DeaDDFuze/DSLITE_Remastered/schematic/original/C-USG-CPU-10.sch

## EAGLE design schematic/original/C-USG-CPU-10.sch (2026-09-28)

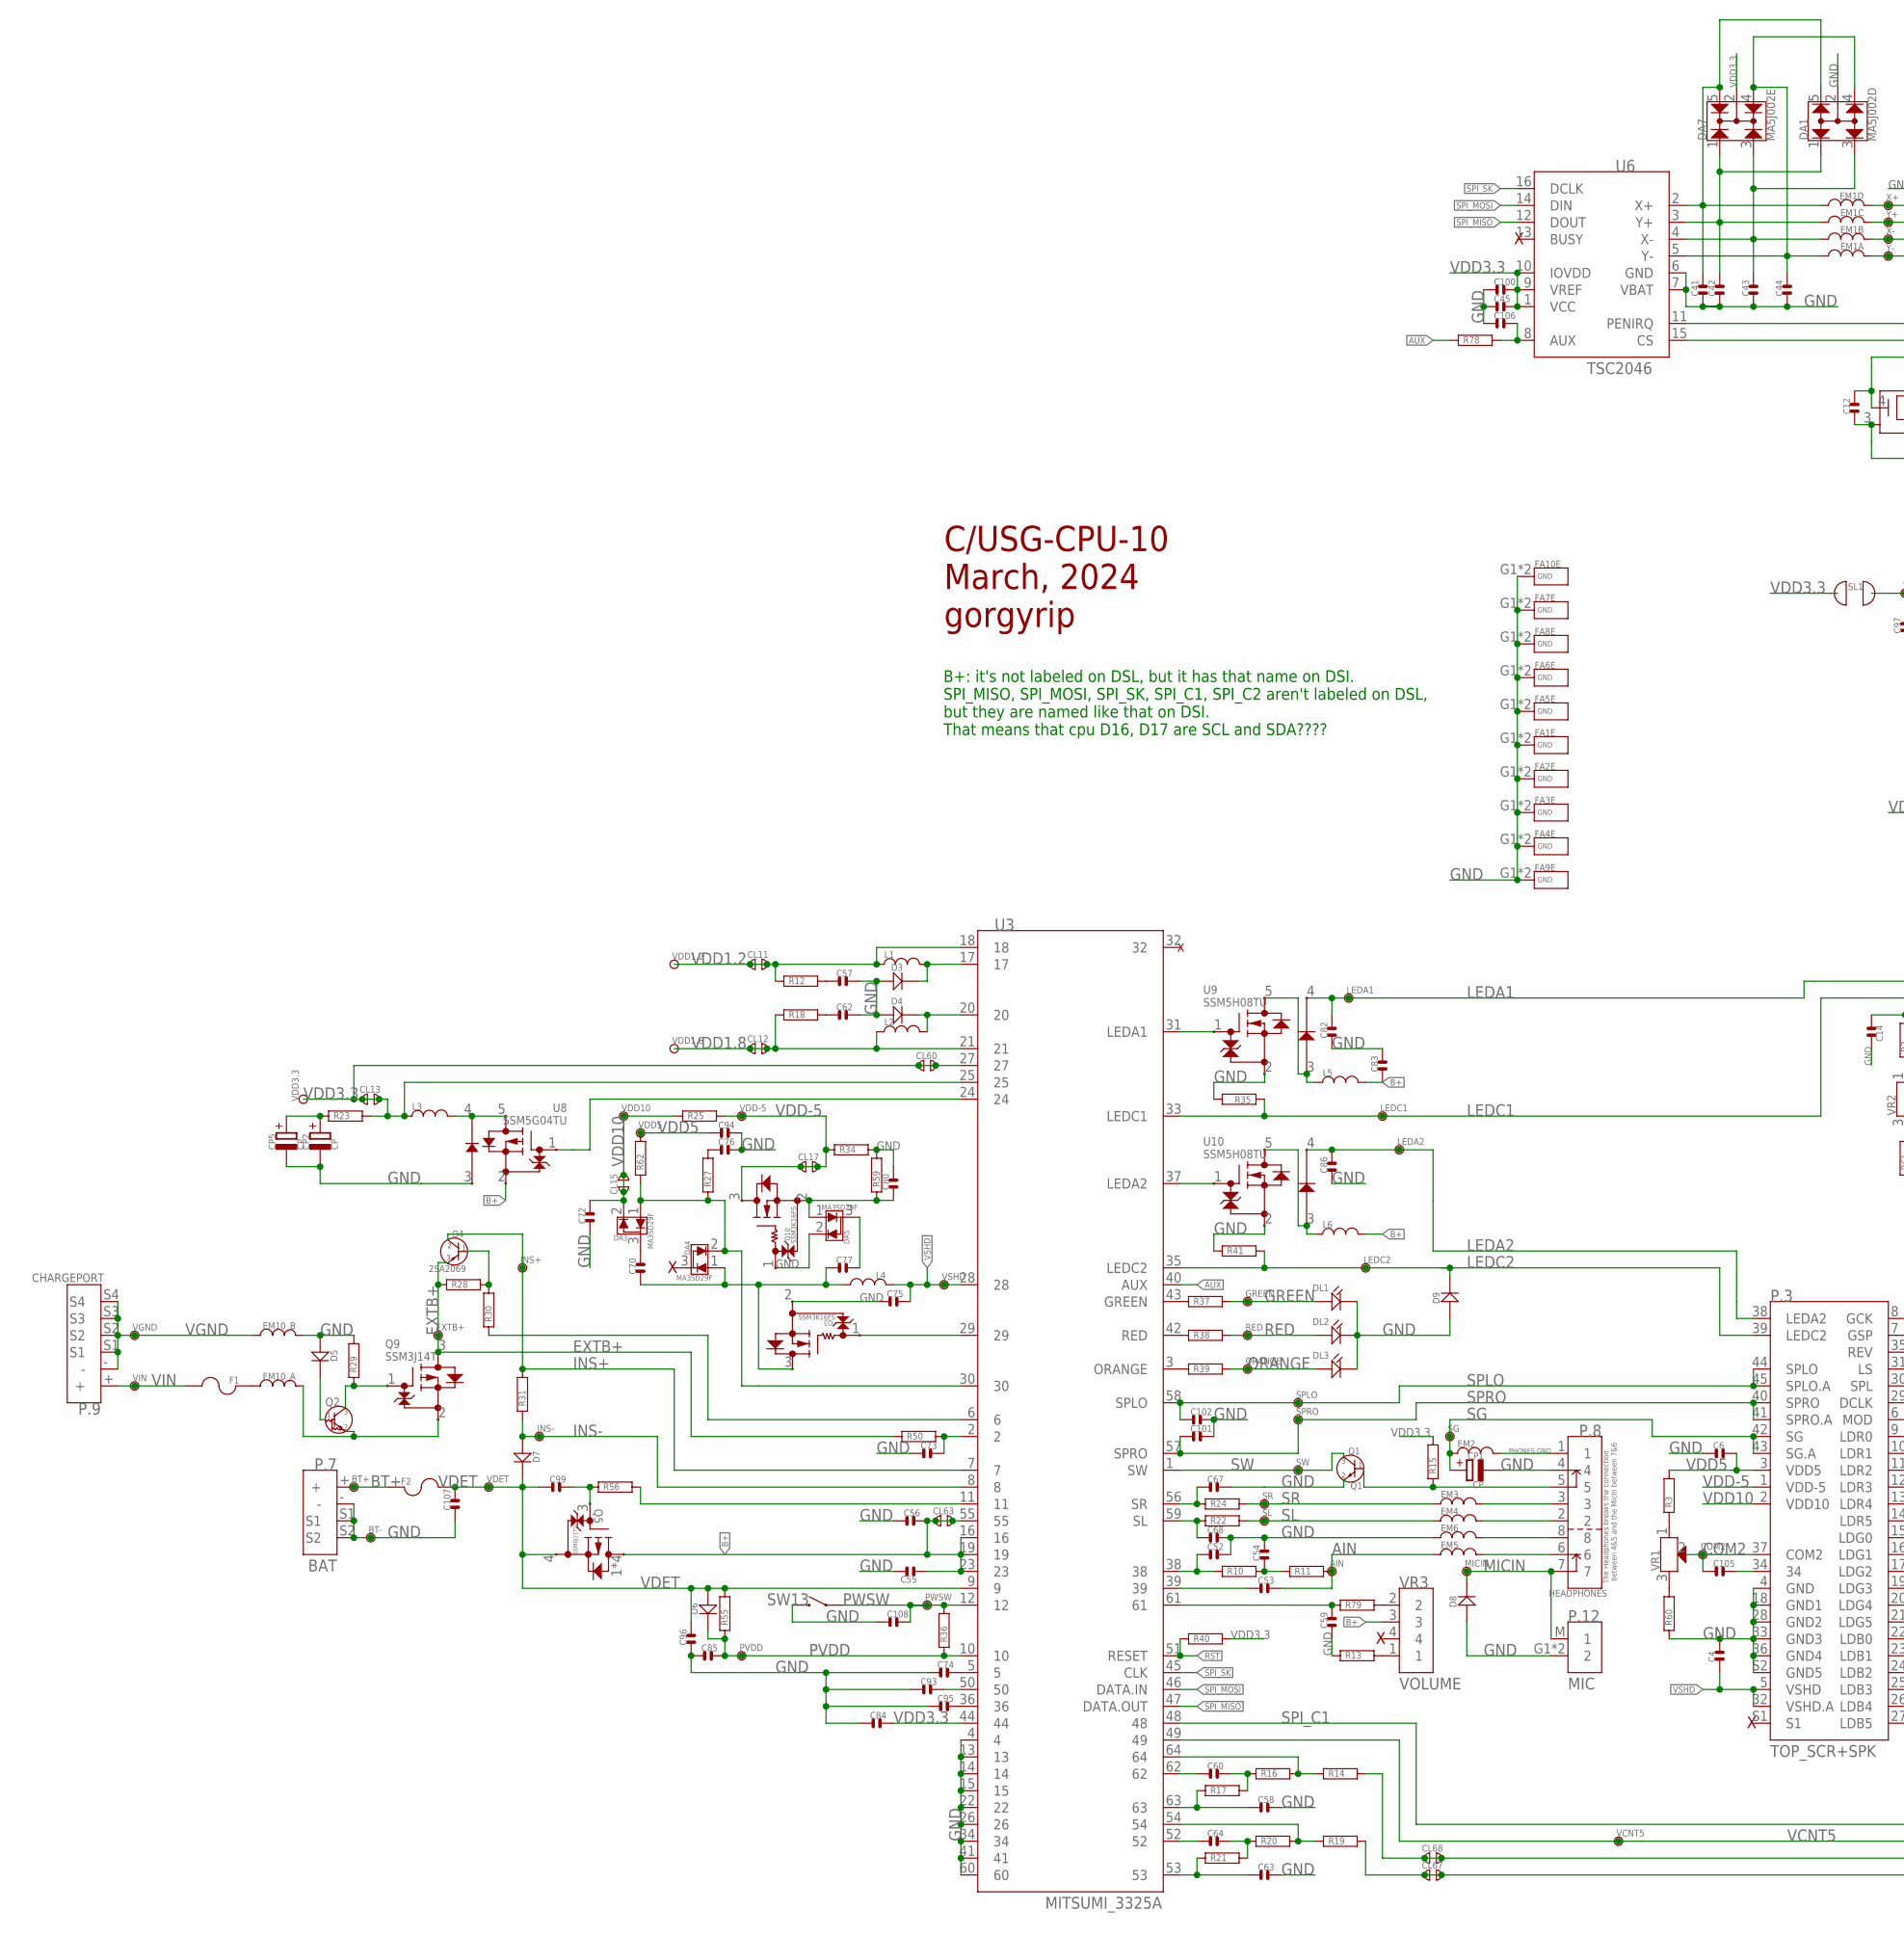
[picture p8: schematic C-USG-CPU-10.sch, part in row 1, column 1]

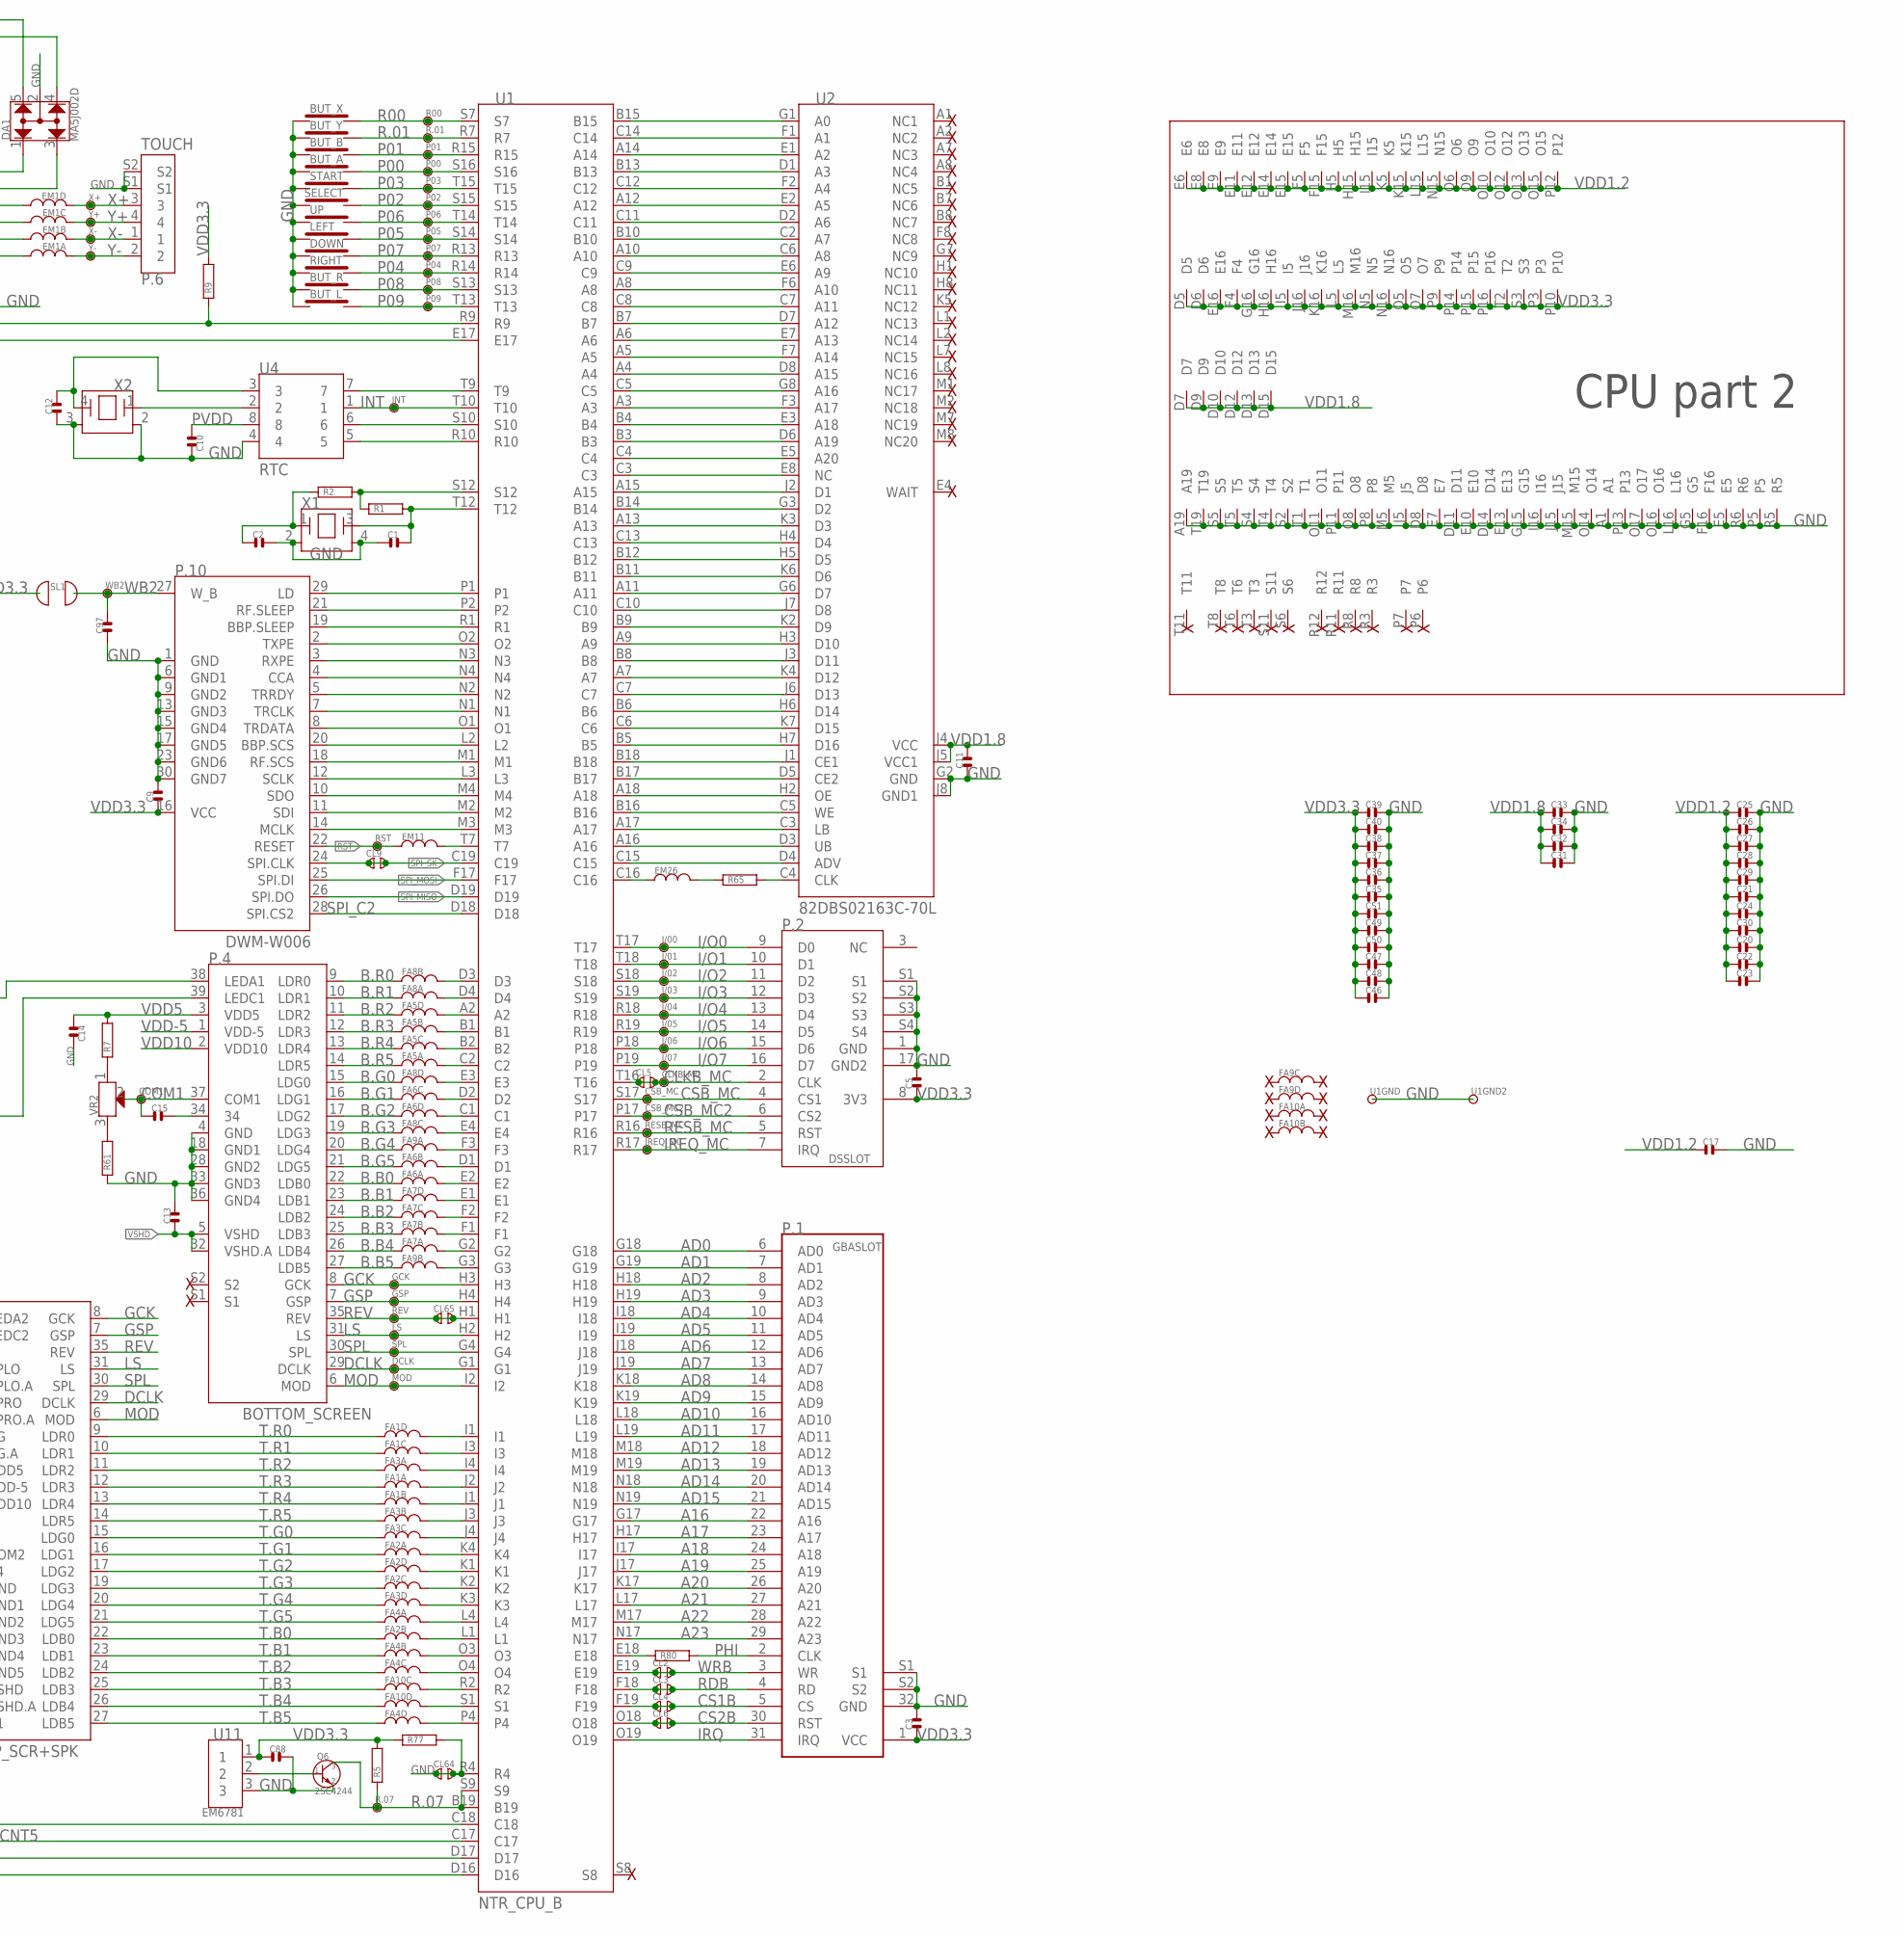
[picture p9: schematic C-USG-CPU-10.sch, part in row 1, column 2]

Parts:
AIN: TP
BT+: TP
BT-: TP
BUT_A: BUT_ABXY; BUTTONSABXY
BUT_B: BUT_ABXY; BUTTONSABXY
BUT_L: SHOULDER_BUT
BUT_R: SHOULDER_BUT
BUT_X: BUT_ABXY; BUTTONSABXY
BUT_Y: BUT_ABXY; BUTTONSABXY
C1, C2, C3, C4, C5, C6, C10, C11, C12, C13, C14, C17, C41, C42, C43, C44, C45, C52, C53, C56, C58, C59, C60, C63, C64, C67, C68, C70, C74, C75, C77, C84, C88, C93, C96, C97, C99, C100, C101, C102, C106, C107, C108: C0402; 0402
C9, C15, C54, C55, C57, C62, C72, C76, C82, C83, C86, C94, C105: C0805; 0805
C20, C21, C22, C23, C24, C25, C26, C27, C28, C29, C30, C31, C32, C33, C34, C35, C36, C37, C38, C39, C40, C46, C47, C48, C49, C50, C51: C0201; 0201
C73, C80, C85, C95: C0603; 0603
CL2, CL3, CL4, CL5, CL6, CL9, CL11, CL12, CL13, CL15, CL17, CL60, CL63, CL64, CL65, CL67, CL68: CL; CL0402
CLKB_MC: TP
COM1, COM2: TP
CP1, CP2, CP5: CP
CSB_MC, CSB_MC2: TP
D3, D4: D3.4
D5, D9: D5
D6: D6
D7: D7
D8: D8
DA1: MA5J002D; DA
DA3, DA4, DA5: MA3SD29F
DA7: MA5J002E; DA
DCLK: TP
DL1, DL2, DL3: DL
DOWN: DPAD
EM1: FILTER_NETWORK
EM2, EM3, EM4, EM5, EM6: FILTER0603; 0603
EM10: EM10
EM11, EM26: FILTER; 0402
EXTB+: TP
F1, F2: FUSE
FA1, FA2, FA3, FA4, FA5, FA6, FA7, FA8, FA9, FA10: FA
GCK: TP
GREEN: TP
GSP: TP
I/00, I/01, I/02, I/03, I/04, I/05, I/06, I/07: TP
INS+: TP
INS-: TP
INT: TP
IREQ_MC: TP
L1, L3, L5, L6: INDUCTOR
L2, L4: INDUCTOR_SMALL
LEDA1, LEDA2: TP
LEDC1, LEDC2: TP
LEFT: DPAD
LS: TP
MICIN: TP
MOD: TP
ORANGE: TP
P00, P01, P02, P03, P04, P05, P06, P07, P08, P09: TP
P.1: GBASLOT; GBA
P.2: DSSLOT; DS
P.3: TOP_SCR+SPK
P.4: BOTTOM_SCREEN
P.6: TOUCH; P6
P.7: BAT
P.8: HEADPHONES
P.9: CHARGEPORT
P.10: DWM-W006; DWM--W006
P.12: MIC
PVDD: TP
PWSW: TP
Q1: Q1
Q2: DTA143ZM; SOT723
Q3, Q10: SSM3K16FS; Q3.10
Q4: 2SA2069; SOT89-3
Q5: SSM6J21TU; UF6
Q6: 2SC4244; SOT723
Q9: SSM3J14T; TO236
R00, R.01, R.07: TP
R1, R2, R3, R5, R7, R9, R10, R11, R12, R13, R14, R15, R16, R17, R18, R19, R20, R21, R22, R23, R24, R25, R27, R28, R29, R30, R34, R35, R36, R37, R38, R39, R40, R41, R50, R55, R56, R59, R60, R61, R62, R65, R77, R78, R79, R80: R0402; 0402
R31: R0805; 0805
RED: TP
RESB_MC: TP
REV: TP
RIGHT: DPAD
RST: TP
SELECT: BUTTON_SMALL
SG: TP
SL: TP
SL1: SL1
SPL: TP
SPLO: TP
SPRO: TP
SR: TP
START: BUTTON_SMALL
SW: TP
SW13: SWITCH
U1: NTR_CPU_B; CPU
U1GND, U1GND2: TP
U2: 82DBS02163C-70L; RAM
U3: MITSUMI_3325A
U4: RTC; TSSOP8
U6: TSC2046; TSSOP16
U8: SSM5G04TU; SOT-353F___(UFV)-M
U9, U10: SSM5H08TU; SOT-353F___(UFV)-M
U11: EM6781
UP: DPAD
VCNT5: TP
VDD1.2, VDD1.8, VDD3.3, VDD5, VDD10: TP
VDD-5: TP
VDET: TP
VGND: TP
VIN: TP
VR1, VR2: VR
VR3: VOLUME
VSHD: TP
WB2: TP
X1: X1
X2: X2
X+: TP
X-: TP
Y+: TP
Y-: TP

Connections:
A16: P.1.22 (A16), U1.G17
A17: P.1.23 (A17), U1.H17
A18: P.1.24 (A18), U1.I17
A19: P.1.25 (A19), U1.J17
A20: P.1.26 (A20), U1.K17
A21: P.1.27 (A21), U1.L17
A22: P.1.28 (A22), U1.M17
A23: P.1.29 (A23), U1.N17
AD0: P.1.6 (AD0), U1.G18
AD1: P.1.7 (AD1), U1.G19
AD2: P.1.8 (AD2), U1.H18
AD3: P.1.9 (AD3), U1.H19
AD4: P.1.10 (AD4), U1.I18
AD5: P.1.11 (AD5), U1.I19
AD6: P.1.12 (AD6), U1.J18
AD7: P.1.13 (AD7), U1.J19
AD8: P.1.14 (AD8), U1.K18
AD9: P.1.15 (AD9), U1.K19
AD10: P.1.16 (AD10), U1.L18
AD11: P.1.17 (AD11), U1.L19
AD12: P.1.18 (AD12), U1.M18
AD13: P.1.19 (AD13), U1.M19
AD14: P.1.20 (AD14), U1.N18
AD15: P.1.21 (AD15), U1.N19
AIN: AIN.P$1, C53.2, EM5.1, R11.2
AUX: R78.1, U3.40 (AUX)
B+: C55.1, C56.2, C83.1, CL63.1, CL63.2, L5.P$2, L6.P$2, Q5.1 (D), U3.16, U3.19, U3.23, U3.55, U8.2, VR3.3
B.B0: FA6.1, P.4.22 (LDB0)
B.B1: FA7.7, P.4.23 (LDB1)
B.B2: FA7.5, P.4.24 (LDB2)
B.B3: FA7.3, P.4.25 (LDB3)
B.B4: FA7.1, P.4.26 (LDB4)
B.B5: FA9.3, P.4.27 (LDB5)
B.G0: FA8.7, P.4.15 (LDG0)
B.G1: FA6.5, P.4.16 (LDG1)
B.G2: FA6.7, P.4.17 (LDG2)
B.G3: FA8.5, P.4.19 (LDG3)
B.G4: FA9.1, P.4.20 (LDG4)
B.G5: FA6.3, P.4.21 (LDG5)
B.R0: FA8.3, P.4.9 (LDR0)
B.R1: FA8.1, P.4.10 (LDR1)
B.R2: FA5.7, P.4.11 (LDR2)
B.R3: FA5.3, P.4.12 (LDR3)
B.R4: FA5.5, P.4.13 (LDR4)
B.R5: FA5.1, P.4.14 (LDR5)
BT+: BT+.P$1, F2.1, P.7.+
CLKB_MC: CL5.1, CL5.2, CLKB_MC.P$1, P.2.2 (CLK), U1.T16
COM1: C15.1, COM1.P$1, P.4.37 (COM1), VR2.2
COM2: C105.1, COM2.P$1, P.3.37 (COM2), VR1.2
CS1B: CL4.1, CL4.2, P.1.5 (CS), U1.F19
CS2B: CL6.1, CL6.2, P.1.30 (RST), U1.O18
CSB_MC: CSB_MC.P$1, P.2.4 (CS1), U1.S17
CSB_MC2: CSB_MC2.P$1, P.2.6 (CS2), U1.P17
DCLK: DCLK.P$1, P.3.29 (DCLK), P.4.29 (DCLK), U1.G1
EXTB+: EXTB+.P$1, Q4.3, Q9.3, R28.1, R50.1
GCK: GCK.P$1, P.3.8 (GCK), P.4.8 (GCK), U1.H3
GND: BT-.P$1, BUT_A.1, BUT_B.1, BUT_L.1, BUT_R.1, BUT_X.1, BUT_Y.1, C1.1, C2.2, C3.2, C4.2, C5.2, C6.1, C9.2, C10.2, C11.1, C12.1, C13.2, C14.2, C17.2, C20.2, C21.2, C22.2, C23.2, C24.2, C25.2, C26.2, C27.2, C28.2, C29.2, C30.2, C31.2, C32.2, C33.2, C34.2, C35.2, C36.2, C37.2, C38.2, C39.2, C40.2, C41.1, C42.1, C43.1, C44.1, C45.1, C46.2, C47.2, C48.2, C49.2, C50.2, C51.2, C52.2, C54.2, C55.2, C56.1, C57.2, C58.2, C59.1, C62.2, C63.2, C67.2, C68.2, C72.1, C73.1, C74.1, C75.1, C76.2, C80.2, C82.1, C83.2, C84.1, C85.1, C86.1, C88.2, C93.1, C94.2, C95.1, C96.1, C97.1, C100.1, C101.2, C102.2, C106.1, C107.1, C108.1, CL64.1, CL64.2, CP1.1, CP2.1, CP5.1, D3.A, D4.A, D5.A, D8.A, D9.A, DA1.2, DA5.2, DL1.C, DL2.C, DL3.C, DOWN.1, EM6.1, EM10.3, FA1.G1 (GND), FA2.G1 (GND), FA3.G1 (GND), FA4.G1 (GND), FA5.G1 (GND), FA6.G1 (GND), FA7.G1 (GND), FA8.G1 (GND), FA9.G1 (GND), FA10.G1 (GND), LEFT.1, P.1.32 (GND), P.1.S1, P.1.S2, P.2.1 (GND), P.2.17 (GND2), P.2.S1, P.2.S2, P.2.S3, P.2.S4, P.3.4 (GND), P.3.18 (GND1), P.3.28 (GND2), P.3.33 (GND3), P.3.36 (GND4), P.3.S2 (GND5), P.4.4 (GND), P.4.18 (GND1), P.4.28 (GND2), P.4.33 (GND3), P.4.36 (GND4), P.6.S1, P.6.S2, P.7.-, P.7.S1, P.7.S2, P.8.4, P.10.1 (GND), P.10.6 (GND1), P.10.9 (GND2), P.10.13 (GND3), P.10.15 (GND4), P.10.17 (GND5), P.10.23 (GND6), P.10.30 (GND7), P.12.G1 (2), Q1.2, Q3.2, Q6.2, Q10.1, R13.1, R29.2, R34.2, R35.2, R41.1, R59.2, R60.1, R61.1, R77.2, RIGHT.1, SELECT.2, START.2, SW13.2, U1.A1, U1.A19, U1.D8, U1.D11, U1.D14, U1.E5, U1.E7, U1.E10, U1.E13, U1.F16, U1.G5, U1.G15, U1.I16, U1.J5, U1.J15, U1.L16, U1.M5, U1.M15, U1.O8, U1.O11, U1.O14, U1.O16, U1.O17, U1.P5, U1.P8, U1.P11, U1.P13, U1.R4, U1.R5, U1.R6, U1.S2, U1.S4, U1.S5, U1.T1, U1.T4, U1.T5, U1.T19, U1GND.P$1, U1GND2.P$1, U2.G2 (GND), U2.J8 (GND1), U3.4, U3.13, U3.14, U3.15, U3.22, U3.26, U3.34, U3.41, U3.60, U4.4, U6.6 (GND), U6.7 (VBAT), U8.3, U9.2, U10.2, U11.3, UP.1, X1.2, X1.4, X2.2, X2.3
GREEN: DL1.A, GREEN.P$1, R37.2
GSP: GSP.P$1, P.3.7 (GSP), P.4.7 (GSP), U1.H4
I/O0: I/00.P$1, P.2.9 (D0), U1.T17
I/O1: I/01.P$1, P.2.10 (D1), U1.T18
I/O2: I/02.P$1, P.2.11 (D2), U1.S18
I/O3: I/03.P$1, P.2.12 (D3), U1.S19
I/O4: I/04.P$1, P.2.13 (D4), U1.R18
I/O5: I/05.P$1, P.2.14 (D5), U1.R19
I/O6: I/06.P$1, P.2.15 (D6), U1.P18
I/O7: I/07.P$1, P.2.16 (D7), U1.P19
INS+: INS+.P$1, Q4.2, R31.2, U3.7
INS-: D7.A, INS-.P$1, R31.1, U3.8
INT: INT.P$1, U1.T10, U4.1
IREQ_MC: IREQ_MC.P$1, P.2.7 (IRQ), U1.R17
IRQ: P.1.31 (IRQ), U1.O19
LEDA1: C82.2, LEDA1.P$1, P.4.38 (LEDA1), U9.4
LEDA2: C86.2, LEDA2.P$1, P.3.38 (LEDA2), U10.4
LEDC1: LEDC1.P$1, P.4.39 (LEDC1), R35.1, U3.33 (LEDC1)
LEDC2: D9.C, LEDC2.P$1, P.3.39 (LEDC2), R41.2, U3.35 (LEDC2)
LS: LS.P$1, P.3.31 (LS), P.4.31 (LS), U1.H2
MICIN: D8.C, MICIN.P$1, P.8.7, P.12.M (1)
MOD: MOD.P$1, P.3.6 (MOD), P.4.6 (MOD), U1.I2
unnamed: P.8.5, Q1.1, R15.1
unnamed: C95.2, U3.36
unnamed: C99.2, Q5.3 (G), R56.1
unnamed: C70.2, DA3.3
unnamed: Q6.1, U11.2
unnamed: U1.B15, U2.G1 (A0)
unnamed: C74.2, U3.5
unnamed: U1.C14, U2.F1 (A1)
unnamed: C77.2, DA5.3
unnamed: C62.1, R18.2
unnamed: U1.A14, U2.E1 (A2)
unnamed: EM3.2, P.8.3
unnamed: EM4.2, P.8.2
unnamed: R9.1, U1.R9, U6.11 (PENIRQ)
unnamed: C67.1, R24.1, U3.56 (SR)
unnamed: C68.1, R22.1, U3.59 (SL)
unnamed: U1.B13, U2.D1 (A3)
unnamed: R37.1, U3.43 (GREEN)
unnamed: U1.C12, U2.F2 (A4)
unnamed: U1.A12, U2.E2 (A5)
unnamed: U1.C11, U2.D2 (A6)
unnamed: U1.B10, U2.C2 (A7)
unnamed: R56.2, U3.11
unnamed: U1.A10, U2.C6 (A8)
unnamed: C58.1, R17.1, U3.63
unnamed: U1.C9, U2.E6 (A9)
unnamed: C64.1, U3.52
unnamed: U1.A8, U2.F6 (A10)
unnamed: FA8.4, U1.D3
unnamed: U1.E17, U6.15 (CS)
unnamed: C93.2, U3.50
unnamed: U1.T9, U4.7
unnamed: C42.2, DA1.1, DA7.1, EM1.6, U6.3 (Y+)
unnamed: U1.C8, U2.C7 (A11)
unnamed: U1.B7, U2.D7 (A12)
unnamed: R80.1, U1.E18
unnamed: U4.2, X2.1
unnamed: C106.2, R78.2, U6.8 (AUX)
unnamed: C43.2, DA1.3, DA7.3, EM1.4, U6.4 (X-)
unnamed: C44.2, DA1.4, DA7.4, EM1.2, U6.5 (Y-)
unnamed: U1.S10, U4.6
unnamed: C41.2, DA1.5, DA7.5, EM1.8, U6.2 (X+)
unnamed: U1.R10, U4.5
unnamed: C12.2, U4.3, X2.4
unnamed: R1.1, R2.2, U1.S12
unnamed: C1.2, R1.2, U1.T12, X1.3
unnamed: P.10.29 (LD), U1.P1
unnamed: C2.1, R2.1, X1.1
unnamed: P.10.21 (RF.SLEEP), U1.P2
unnamed: P.10.19 (BBP.SLEEP), U1.R1
unnamed: P.10.2 (TXPE), U1.O2
unnamed: P.10.3 (RXPE), U1.N3
unnamed: P.10.4 (CCA), U1.N4
unnamed: P.10.5 (TRRDY), U1.N2
unnamed: P.10.7 (TRCLK), U1.N1
unnamed: U1.A6, U2.E7 (A13)
unnamed: P.10.8 (TRDATA), U1.O1
unnamed: U1.A5, U2.F7 (A14)
unnamed: P.10.20 (BBP.SCS), U1.L2
unnamed: U1.A4, U2.D8 (A15)
unnamed: U1.C5, U2.G8 (A16)
unnamed: U1.A3, U2.F3 (A17)
unnamed: U1.B4, U2.E3 (A18)
unnamed: U1.B3, U2.D6 (A19)
unnamed: C63.1, R21.1, U3.53
unnamed: U1.C4, U2.E5 (A20)
unnamed: U1.C3, U2.E8 (NC)
unnamed: U1.A15, U2.J2 (D1)
unnamed: EM10.2, F1.1
unnamed: Q2.3, Q9.1, R29.1
unnamed: C52.1, R10.1, U3.38
unnamed: U1.B14, U2.G3 (D2)
unnamed: U1.A13, U2.K3 (D3)
unnamed: P.10.10 (SDO), U1.M4
unnamed: C70.1, C77.1, DA4.1, L4.2, Q3.3
unnamed: FA8.2, U1.D4
unnamed: P.10.11 (SDI), U1.M2
unnamed: P.10.18 (RF.SCS), U1.M1
unnamed: U1.C13, U2.H4 (D4)
unnamed: P.10.12 (SCLK), U1.L3
unnamed: C73.2, R50.2, U3.2
unnamed: P.10.14 (MCLK), U1.M3
unnamed: EM11.2, U1.T7
unnamed: FA5.8, U1.A2
unnamed: U1.B12, U2.H5 (D5)
unnamed: FA5.4, U1.B1
unnamed: FA5.6, U1.B2
unnamed: FA5.2, U1.C2
unnamed: U1.B11, U2.K6 (D6)
unnamed: FA8.8, U1.E3
unnamed: FA6.6, U1.D2
unnamed: U1.A11, U2.G6 (D7)
unnamed: FA6.8, U1.C1
unnamed: FA8.6, U1.E4
unnamed: FA9.2, U1.F3
unnamed: R39.1, U3.3 (ORANGE)
unnamed: U1.C10, U2.J7 (D8)
unnamed: FA6.4, U1.D1
unnamed: C54.1, R10.2, R11.1
unnamed: U1.B9, U2.K2 (D9)
unnamed: Q3.1, U3.29
unnamed: C53.1, U3.39
unnamed: U1.A9, U2.H3 (D10)
unnamed: U1.B8, U2.J3 (D11)
unnamed: U1.A7, U2.K4 (D12)
unnamed: C64.2, R20.1, R21.2
unnamed: U1.C7, U2.J6 (D13)
unnamed: FA6.2, U1.E2
unnamed: FA7.8, U1.E1
unnamed: FA7.6, U1.F2
unnamed: FA7.4, U1.F1
unnamed: FA7.2, U1.G2
unnamed: FA9.4, U1.G3
unnamed: FA1.8, U1.I1
unnamed: FA1.6, U1.I3
unnamed: FA3.2, U1.I4
unnamed: R13.2, VR3.1
unnamed: U1.B6, U2.H6 (D14)
unnamed: U1.C6, U2.K7 (D15)
unnamed: D5.C, Q2.1
unnamed: EM10.1, Q2.2, Q9.2
unnamed: Q4.1, R28.2, R30.2
unnamed: U1.B5, U2.H7 (D16)
unnamed: FA1.2, U1.J2
unnamed: U1.B18, U2.J1 (CE1)
unnamed: C59.2, R79.1, U3.61
unnamed: FA1.4, U1.J1
unnamed: U1.B17, U2.D5 (CE2)
unnamed: U1.A18, U2.H2 (OE)
unnamed: U1.B16, U2.C5 (WE)
unnamed: U1.A17, U2.C3 (LB)
unnamed: U1.A16, U2.D3 (UB)
unnamed: FA3.4, U1.J3
unnamed: FA3.6, U1.J4
unnamed: FA2.2, U1.K4
unnamed: FA2.8, U1.K1
unnamed: FA2.6, U1.K2
unnamed: U1.C15, U2.D4 (ADV)
unnamed: EM26.1, U1.C16
unnamed: EM26.2, R65.1
unnamed: R65.2, U2.C4 (CLK)
unnamed: FA3.8, U1.K3
unnamed: FA4.2, U1.L4
unnamed: FA2.4, U1.L1
unnamed: R7.1, VR2.1
unnamed: FA4.4, U1.O3
unnamed: FA4.6, U1.O4
unnamed: FA10.6, U1.R2
unnamed: FA10.8, U1.S1
unnamed: FA4.8, U1.P4
unnamed: C15.2, P.4.34
unnamed: R61.2, VR2.3
unnamed: R3.1, VR1.1
unnamed: C105.2, P.3.34
unnamed: R60.2, VR1.3
unnamed: R19.1, R20.2, U3.54
unnamed: CL67.1, CL67.2, R19.2, U1.D16
unnamed: C60.2, R16.1, R17.2
unnamed: C60.1, U3.62
unnamed: R14.1, R16.2, U3.64
unnamed: CL68.1, CL68.2, R14.2, U1.D17
unnamed: R79.2, VR3.2
unnamed: U3.31 (LEDA1), U9.1
unnamed: U3.37 (LEDA2), U10.1
unnamed: L5.P$1, U9.3, U9.5
unnamed: R38.1, U3.42 (RED)
unnamed: L6.P$1, U10.3, U10.5
unnamed: EM6.2, P.8.8
unnamed: EM5.2, P.8.6
unnamed: R30.1, U3.6
unnamed: C80.1, DA5.1, Q10.2, R59.1
unnamed: DA3.1, DA4.2, R27.1, R62.1, U3.30
unnamed: C76.1, R27.2
unnamed: L3.P$2, U8.4, U8.5
unnamed: CP2.2, CP5.2, R23.1
unnamed: U3.24, U8.1
unnamed: D4.C, L2.2, U3.20
unnamed: C57.1, R12.2
unnamed: D3.C, L1.P$2, U3.17
ORANGE: DL3.A, ORANGE.P$1, R39.2
P00: BUT_A.2, P00.P$1, U1.S16
P01: BUT_B.2, P01.P$1, U1.R15
P02: P02.P$1, SELECT.1, U1.S15
P03: P03.P$1, START.1, U1.T15
P04: P04.P$1, RIGHT.2, U1.R14
P05: LEFT.2, P05.P$1, U1.S14
P06: P06.P$1, U1.T14, UP.2
P07: DOWN.2, P07.P$1, U1.R13
P08: BUT_R.2, P08.P$1, U1.S13
P09: BUT_L.2, P09.P$1, U1.T13
PHI: P.1.2 (CLK), R80.2
PHONES.GND: EM2.2, P.8.1
PVDD: C10.1, C85.2, D6.C, PVDD.P$1, R36.1, R55.1, U3.10, U4.8
PWSW: C108.2, PWSW.P$1, R36.2, SW13.1, U3.12
R00: BUT_X.2, R00.P$1, U1.S7
R.01: BUT_Y.2, R.01.P$1, U1.R7
R.07: Q6.3, R5.1, R.07.P$1, U1.B19, U1.S9
RDB: CL3.1, CL3.2, P.1.4 (RD), U1.F18
RED: DL2.A, R38.2, RED.P$1
RESB_MC: P.2.5 (RST), RESB_MC.P$1, U1.R16
REV: CL65.1, CL65.2, P.3.35 (REV), P.4.35 (REV), REV.P$1, U1.H1
RST: EM11.1, P.10.22 (RESET), R40.1, RST.P$1, U3.51 (RESET)
SG: CP1.2, EM2.1, P.3.42 (SG), P.3.43 (SG.A), SG.P$1
SL: EM4.1, R22.2, SL.P$1
SPI_C1: U1.C18, U3.48
SPI_C2: P.10.28 (SPI.CS2), U1.D18
SPI_MISO: P.10.26 (SPI.DO), U1.D19, U3.47 (DATA.OUT), U6.12 (DOUT)
SPI_MOSI: P.10.25 (SPI.DI), U1.F17, U3.46 (DATA.IN), U6.14 (DIN)
SPI_SK: CL9.1, CL9.2, P.10.24 (SPI.CLK), U1.C19, U3.45 (CLK), U6.16 (DCLK)
SPL: P.3.30 (SPL), P.4.30 (SPL), SPL.P$1, U1.G4
SPLO: C102.1, P.3.44 (SPLO), P.3.45 (SPLO.A), SPLO.P$1, U3.58 (SPLO)
SPRO: C101.1, P.3.40 (SPRO), P.3.41 (SPRO.A), SPRO.P$1, U3.57 (SPRO)
SR: EM3.1, R24.2, SR.P$1
SW: Q1.3, SW.P$1, U3.1 (SW)
T.B0: FA2.3, P.3.22 (LDB0)
T.B1: FA4.3, P.3.23 (LDB1)
T.B2: FA4.5, P.3.24 (LDB2)
T.B3: FA10.5, P.3.25 (LDB3)
T.B4: FA10.7, P.3.26 (LDB4)
T.B5: FA4.7, P.3.27 (LDB5)
T.G0: FA3.5, P.3.15 (LDG0)
T.G1: FA2.1, P.3.16 (LDG1)
T.G2: FA2.7, P.3.17 (LDG2)
T.G3: FA2.5, P.3.19 (LDG3)
T.G4: FA3.7, P.3.20 (LDG4)
T.G5: FA4.1, P.3.21 (LDG5)
T.R0: FA1.7, P.3.9 (LDR0)
T.R1: FA1.5, P.3.10 (LDR1)
T.R2: FA3.1, P.3.11 (LDR2)
T.R3: FA1.1, P.3.12 (LDR3)
T.R4: FA1.3, P.3.13 (LDR4)
T.R5: FA3.3, P.3.14 (LDR5)
VCNT5: U1.C17, U3.49, VCNT5.P$1
VDD1.2: C17.1, C20.1, C21.1, C22.1, C23.1, C24.1, C25.1, C26.1, C27.1, C28.1, C29.1, C30.1, CL11.1, CL11.2, L1.P$1, R12.1, U1.E6, U1.E8, U1.E9, U1.E11, U1.E12, U1.E14, U1.E15, U1.F5, U1.F15, U1.H5, U1.H15, U1.I15, U1.K5, U1.K15, U1.L15, U1.N15, U1.O6, U1.O9, U1.O10, U1.O12, U1.O13, U1.O15, U1.P12, U3.18, VDD1.2.P$1
VDD1.8: C11.2, C31.1, C32.1, C33.1, C34.1, CL12.1, CL12.2, L2.1, R18.1, U1.D7, U1.D9, U1.D10, U1.D12, U1.D13, U1.D15, U2.J4 (VCC), U2.J5 (VCC1), U3.21, VDD1.8.P$1
VDD3.3: C3.1, C5.1, C9.1, C35.1, C36.1, C37.1, C38.1, C39.1, C40.1, C45.2, C46.1, C47.1, C48.1, C49.1, C50.1, C51.1, C84.2, C88.1, C100.2, CL13.1, CL13.2, CL60.1, CL60.2, DA7.2, L3.P$1, P.1.1 (VCC), P.2.8 (3V3), P.10.16 (VCC), R5.2, R9.2, R15.2, R23.2, R40.2, R77.1, SL1.P$2, U1.D5, U1.D6, U1.E16, U1.F4, U1.G16, U1.H16, U1.I5, U1.J16, U1.K16, U1.L5, U1.M16, U1.N5, U1.N16, U1.O5, U1.O7, U1.P3, U1.P9, U1.P10, U1.P14, U1.P15, U1.P16, U1.S3, U1.T2, U3.25, U3.27, U3.44, U6.1 (VCC), U6.9 (VREF), U6.10 (IOVDD), U11.1, VDD3.3.P$1
VDD5: C6.2, C14.1, C94.1, P.3.3 (VDD5), P.4.3 (VDD5), R3.2, R7.2, R62.2, VDD5.P$1
VDD10: C72.2, CL15.1, CL15.2, DA3.2, P.3.2 (VDD10), P.4.2 (VDD10), R25.1, VDD10.P$1
VDD-5: CL17.1, CL17.2, P.3.1 (VDD-5), P.4.1 (VDD-5), Q10.3, R25.2, R34.1, VDD-5.P$1
VDET: C96.2, C99.1, C107.2, D6.A, D7.C, F2.2, Q5.4 (S), R55.2, U3.9, VDET.P$1
VGND: EM10.4, P.9.-, P.9.S1, P.9.S2, P.9.S3, P.9.S4, VGND.P$1
VIN: F1.2, P.9.+, VIN.P$1
VSHD: C4.1, C13.1, C75.2, L4.1, P.3.5 (VSHD), P.3.32 (VSHD.A), P.4.5 (VSHD), P.4.32 (VSHD.A), U3.28, VSHD.P$1
WB2: C97.2, P.10.27 (W_B), SL1.P$1, WB2.P$1
WRB: CL2.1, CL2.2, P.1.3 (WR), U1.E19
X+: EM1.7, P.6.3, X+.P$1
X-: EM1.3, P.6.1, X-.P$1
Y+: EM1.5, P.6.4, Y+.P$1
Y-: EM1.1, P.6.2, Y-.P$1

Notes on the sheet:
C/USG-CPU-10 March, 2024 gorgyrip
B+: it's not labeled on DSL, but it has that name on DSI. SPI_MISO, SPI_MOSI, SPI_SK, SPI_C1, SPI_C2 aren't labeled on DSL, but they are named like that on DSI. That means that cpu D16, D17 are SCL and SDA????
